mavory/Arduino-Environmental-Alert-System/Photos/20251206_211413.jpg

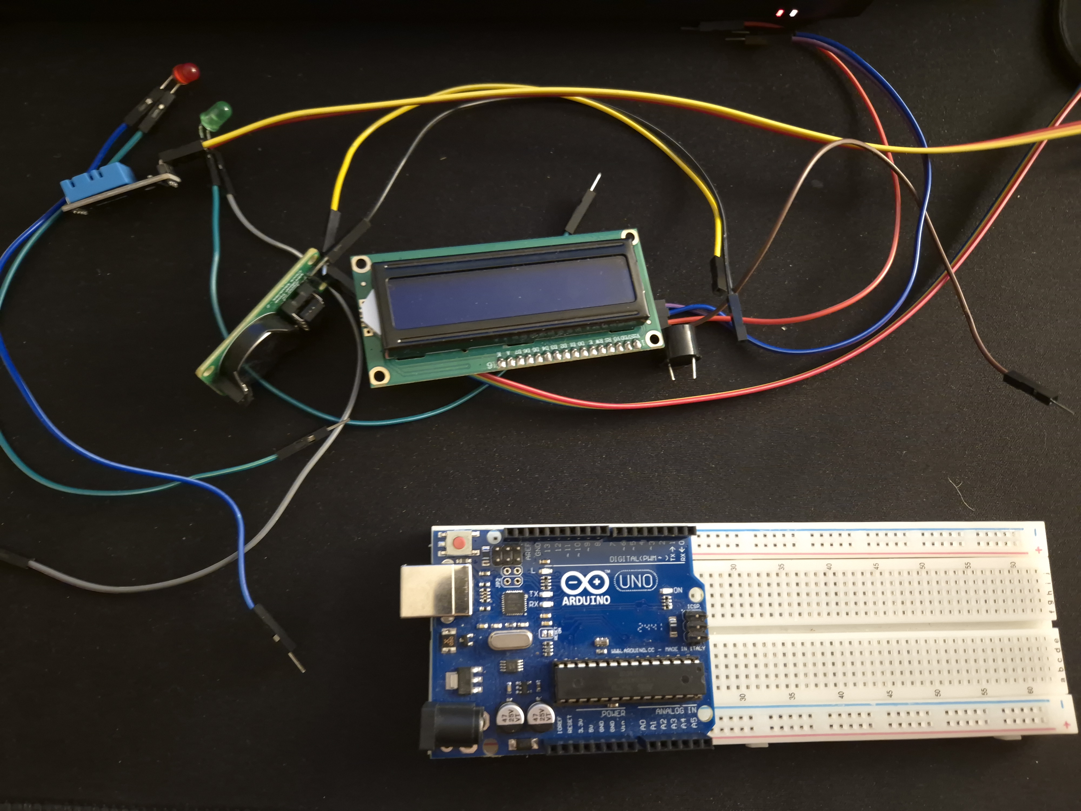
Photos/20251206_211413.jpg
