mavory/Arduino-Environmental-Alert-System/Photos/20251206_214523.jpg

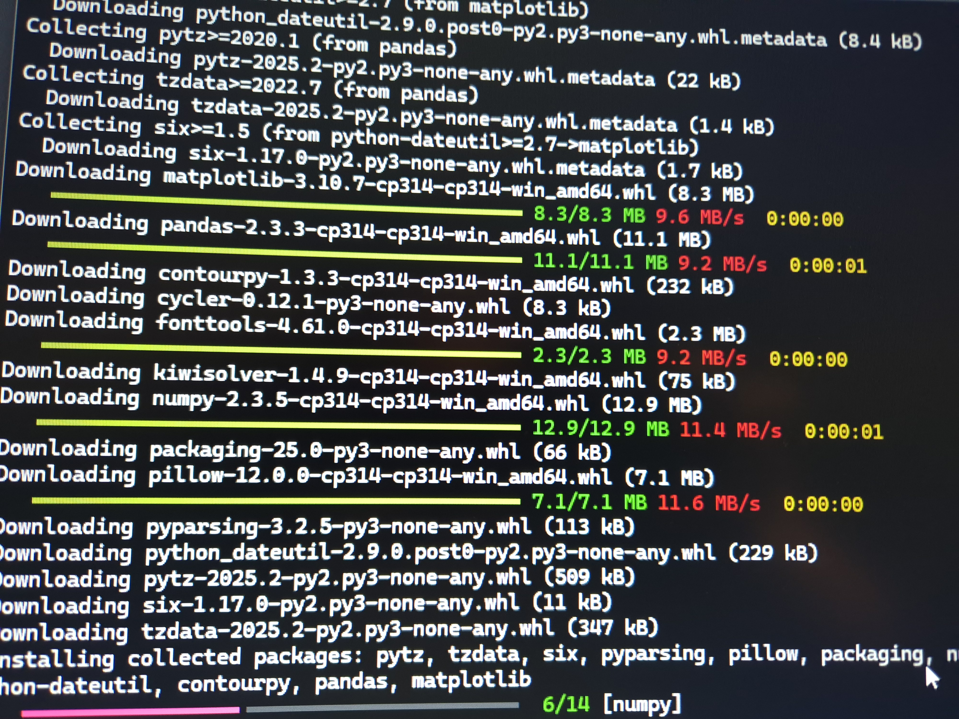
Photos/20251206_214523.jpg
