mavory/Arduino-Environmental-Alert-System/Photos/20251207_101758.jpg

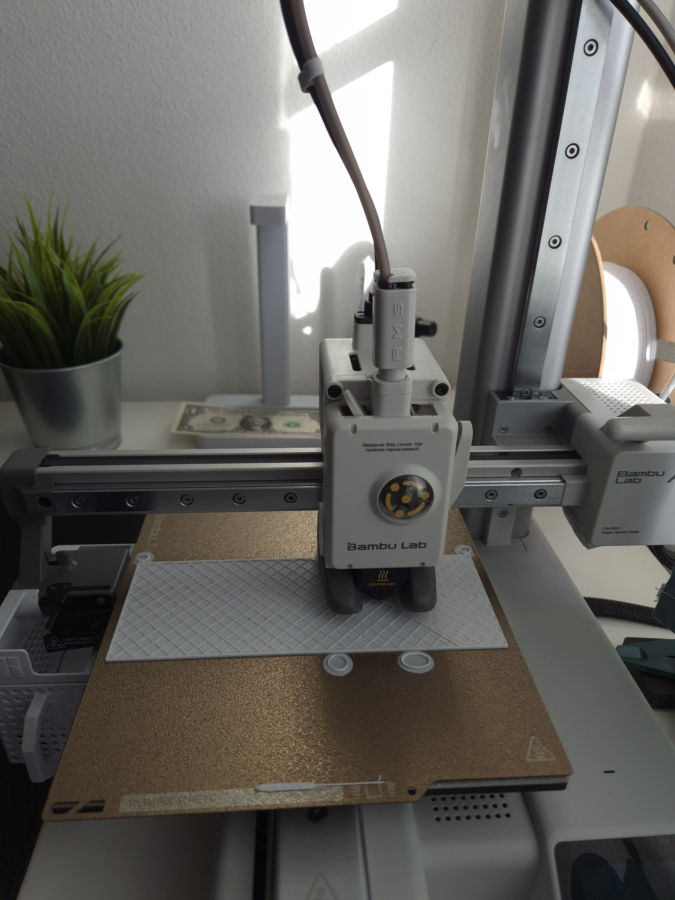
Photos/20251207_101758.jpg
