mavory/Arduino-Environmental-Alert-System/Circuit diagram/Schema.kicad_sch

## KiCad design Circuit diagram/Schema.kicad_sch (2025-12-09)

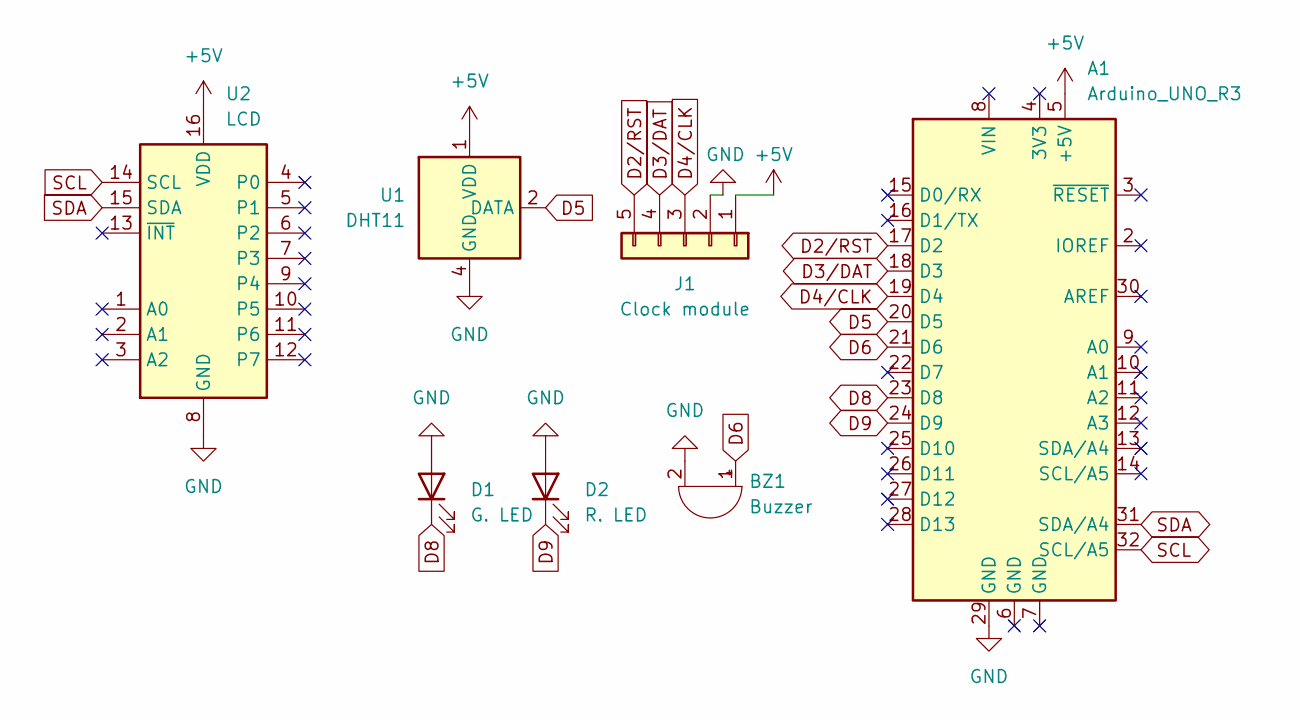
[picture p12: schematic Schema.kicad_sch]

Parts:
A1: Arduino_UNO_R3
BZ1: Buzzer
D1: G. LED
D2: R. LED
J1: Clock module
U1: DHT11; Aosong_DHT11_5.5x12.0_P2.54mm
U2: LCD; DIP-16_W7.62mm

Connections:
+5V: A1.5 (+5V), J1.1, U1.1 (VDD), U2.16 (VDD)
D2/RST: A1.17 (D2), J1.5
D3/DAT: A1.18 (D3), J1.4
D4/CLK: A1.19 (D4), J1.3
D5: A1.20 (D5), U1.2 (DATA)
D6: A1.21 (D6), BZ1.1 (+)
D8: A1.23 (D8), D1.1 (K)
D9: A1.24 (D9), D2.1 (K)
GND: A1.29 (GND), BZ1.2 (-), D1.2 (A), D2.2 (A), J1.2, U1.4 (GND), U2.8 (GND)
SCL: A1.32 (SCL/A5), U2.14 (SCL)
SDA: A1.31 (SDA/A4), U2.15 (SDA)
